FreeAudioTechnology/fat-violet/capsule/FAT array A/FAT_MEMS_Array_A1_2016-Feb-26_02-34-16AM-000_HOME.png

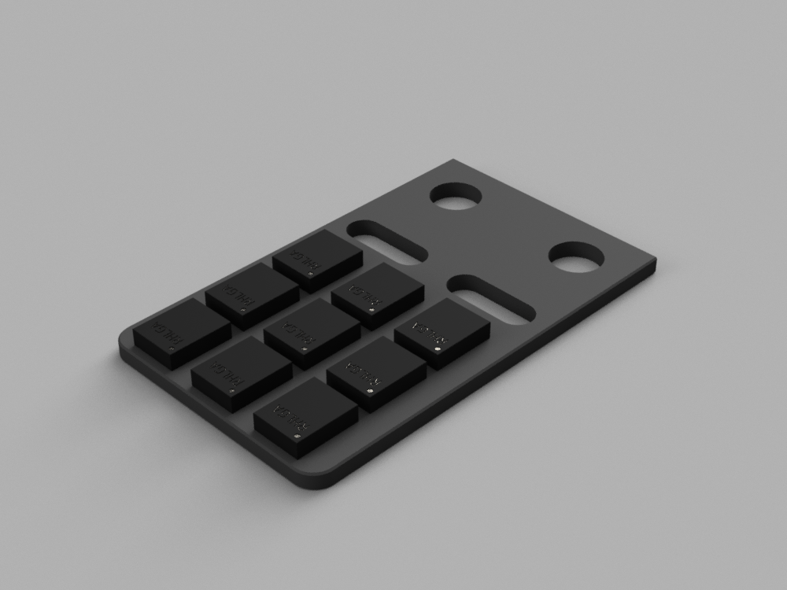
capsule/FAT array A/FAT_MEMS_Array_A1_2016-Feb-26_02-34-16AM-000_HOME.png
