FreeAudioTechnology/fat-violet/capsule/FAT capsule R/FAT Capsule R v2 cut1.png

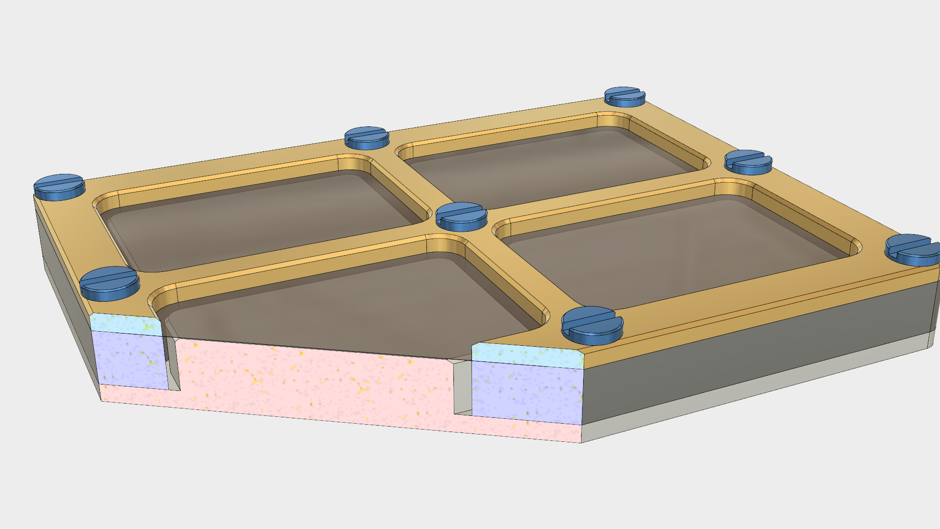
capsule/FAT capsule R/FAT Capsule R v2 cut1.png
