FreeAudioTechnology/fat-violet/capsule/FAT capsule R/FAT Capsule R v2 cut2.png

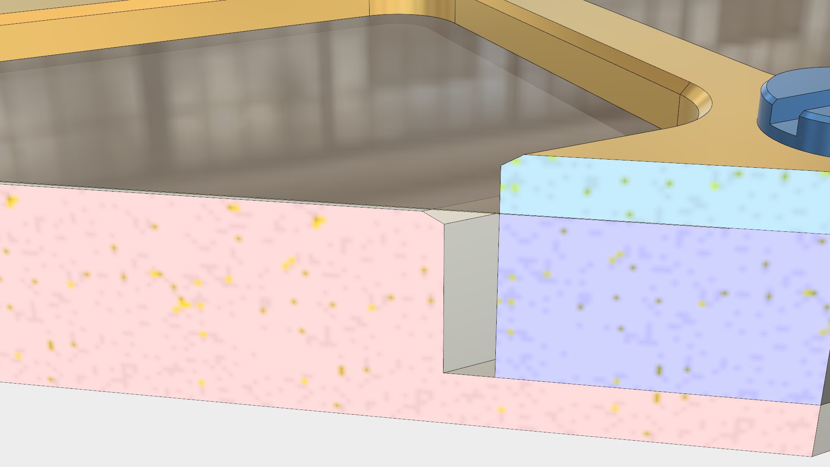
capsule/FAT capsule R/FAT Capsule R v2 cut2.png
