FreeAudioTechnology/fat-violet/capsule/FAT capsule R/FAT Capsule R v3.png

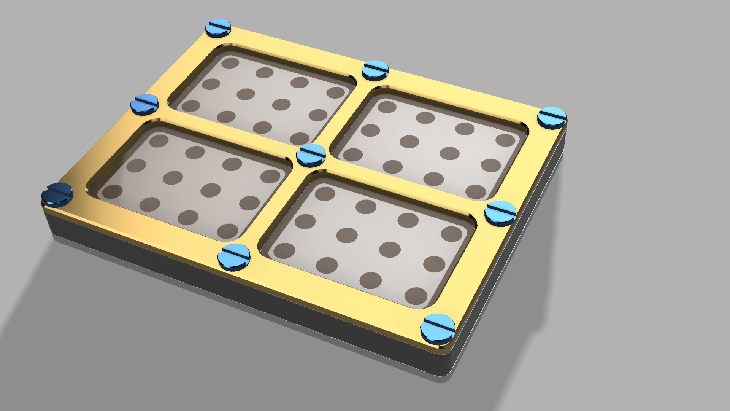
capsule/FAT capsule R/FAT Capsule R v3.png
