FreeAudioTechnology/fat-violet/case/misc/Fanatone Violet Microphone Case 1 v4.png

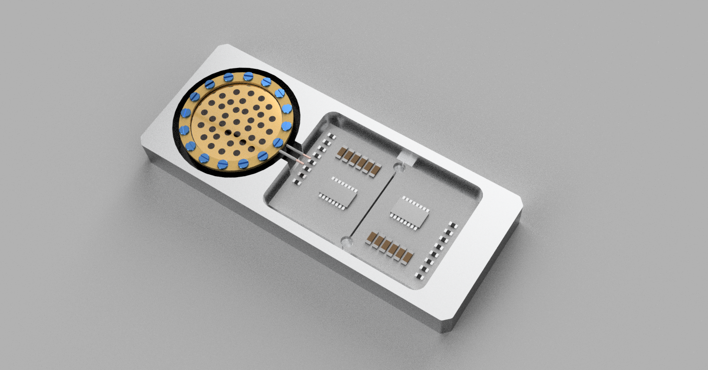
case/misc/Fanatone Violet Microphone Case 1 v4.png
