FreeAudioTechnology/fat-violet/case/misc/Fanatone Violet Microphone Case 1 v5.png

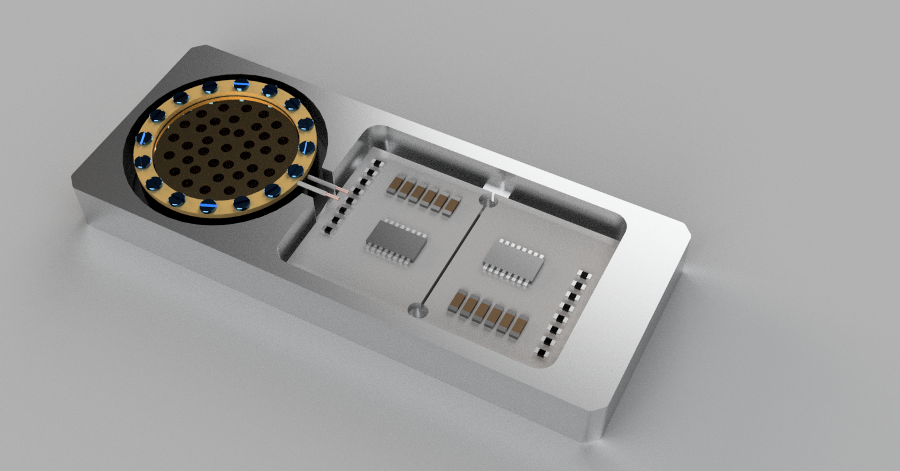
case/misc/Fanatone Violet Microphone Case 1 v5.png
