FreeAudioTechnology/fat-violet/case/misc/Fanatone Violet Microphone Case 1 v7 fibonacci sketch.png

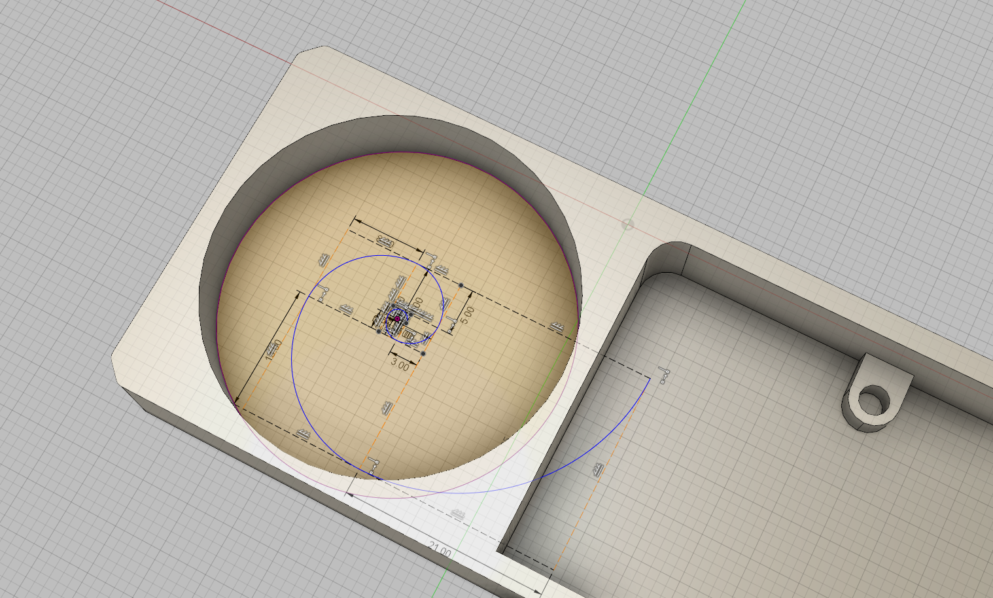
case/misc/Fanatone Violet Microphone Case 1 v7 fibonacci sketch.png
