FreeAudioTechnology/fat-violet/case/misc/Fanatone Violet Microphone Case 1 v7 fibonacci sunflower sketch.png

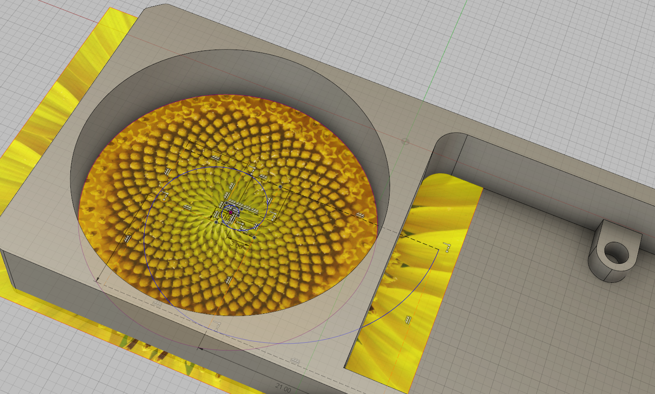
case/misc/Fanatone Violet Microphone Case 1 v7 fibonacci sunflower sketch.png
