FreeAudioTechnology/fat-violet/case/misc/Fanatone Violet Microphone Case 1 v8 hole pattern 1.png

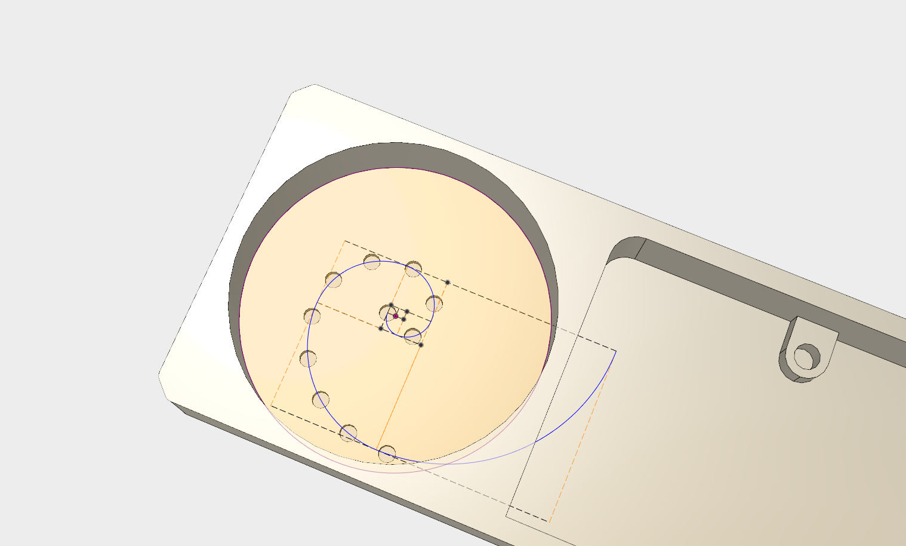
case/misc/Fanatone Violet Microphone Case 1 v8 hole pattern 1.png
