FreeAudioTechnology/fat-violet/case/misc/Fanatone Violet Microphone Case 1 v10 closed.png

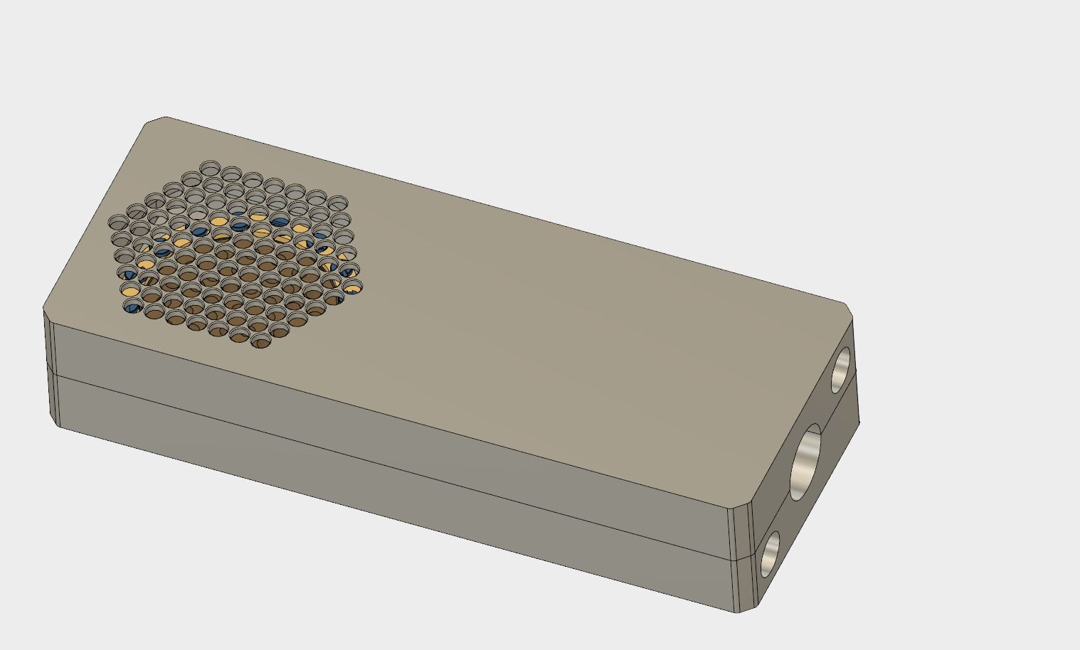
case/misc/Fanatone Violet Microphone Case 1 v10 closed.png
