FreeAudioTechnology/fat-violet/case/misc/Fanatone Violet Microphone Case 2 v2 slotted.png

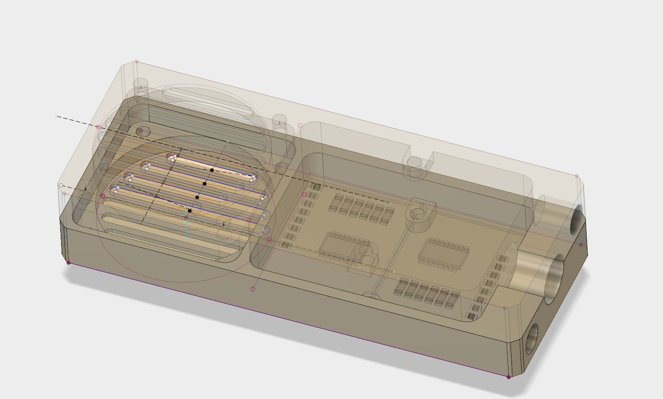
case/misc/Fanatone Violet Microphone Case 2 v2 slotted.png
