FreeAudioTechnology/fat-violet/case/misc/Fanatone Violet Microphone Case 2 v4 raytraced.png

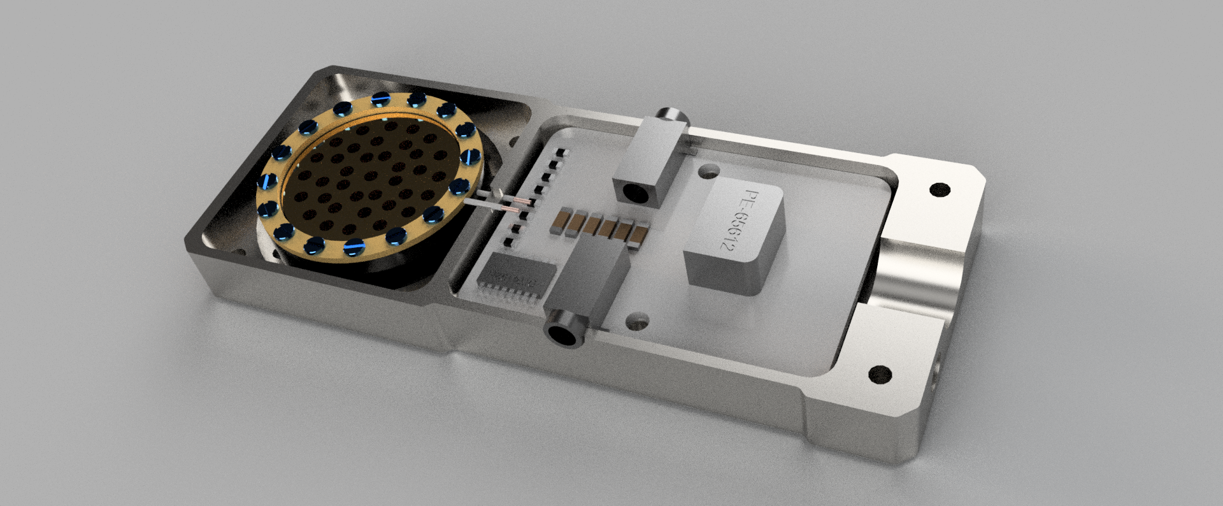
case/misc/Fanatone Violet Microphone Case 2 v4 raytraced.png
