FreeAudioTechnology/fat-violet/case/misc/Fanatone Violet Microphone Case 2 v4 rt bot tagged.png

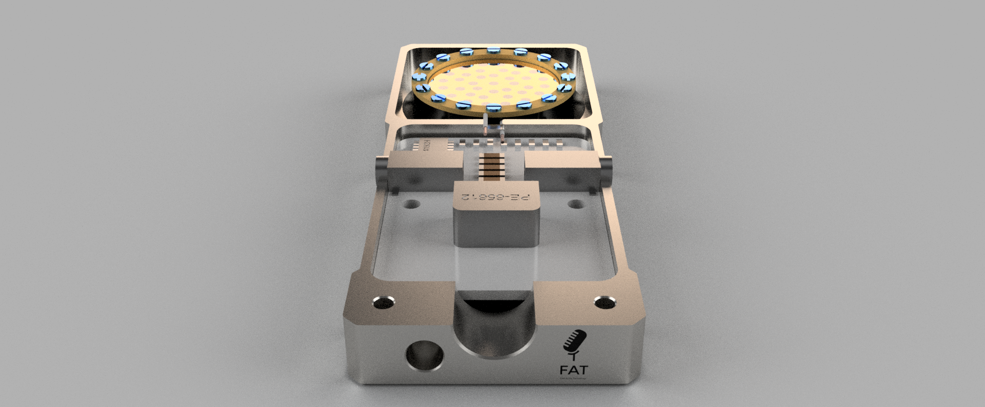
case/misc/Fanatone Violet Microphone Case 2 v4 rt bot tagged.png
