FreeAudioTechnology/fat-violet/case/misc/Fanatone Violet Microphone Case 2 v4 top.png

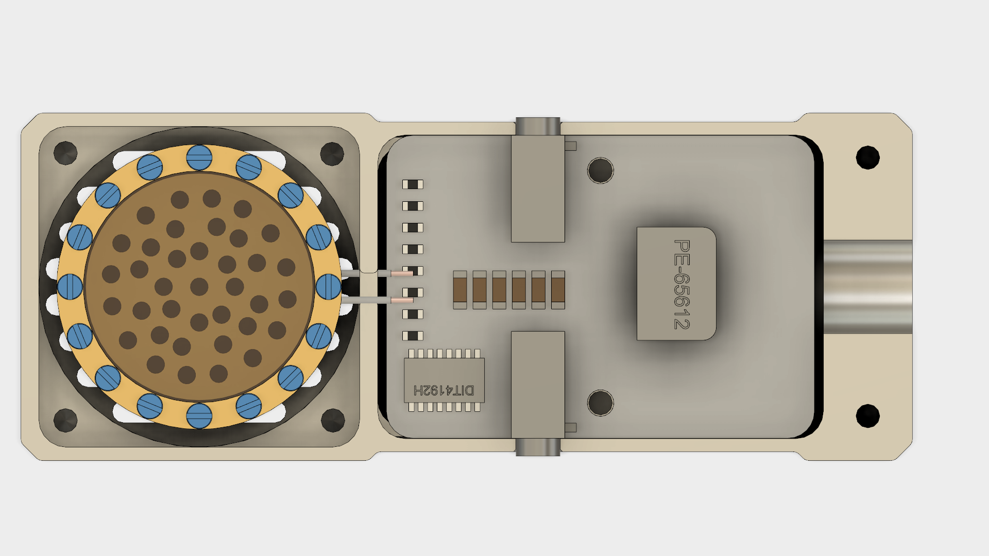
case/misc/Fanatone Violet Microphone Case 2 v4 top.png
