FreeAudioTechnology/fat-violet/pcb/ADC.png

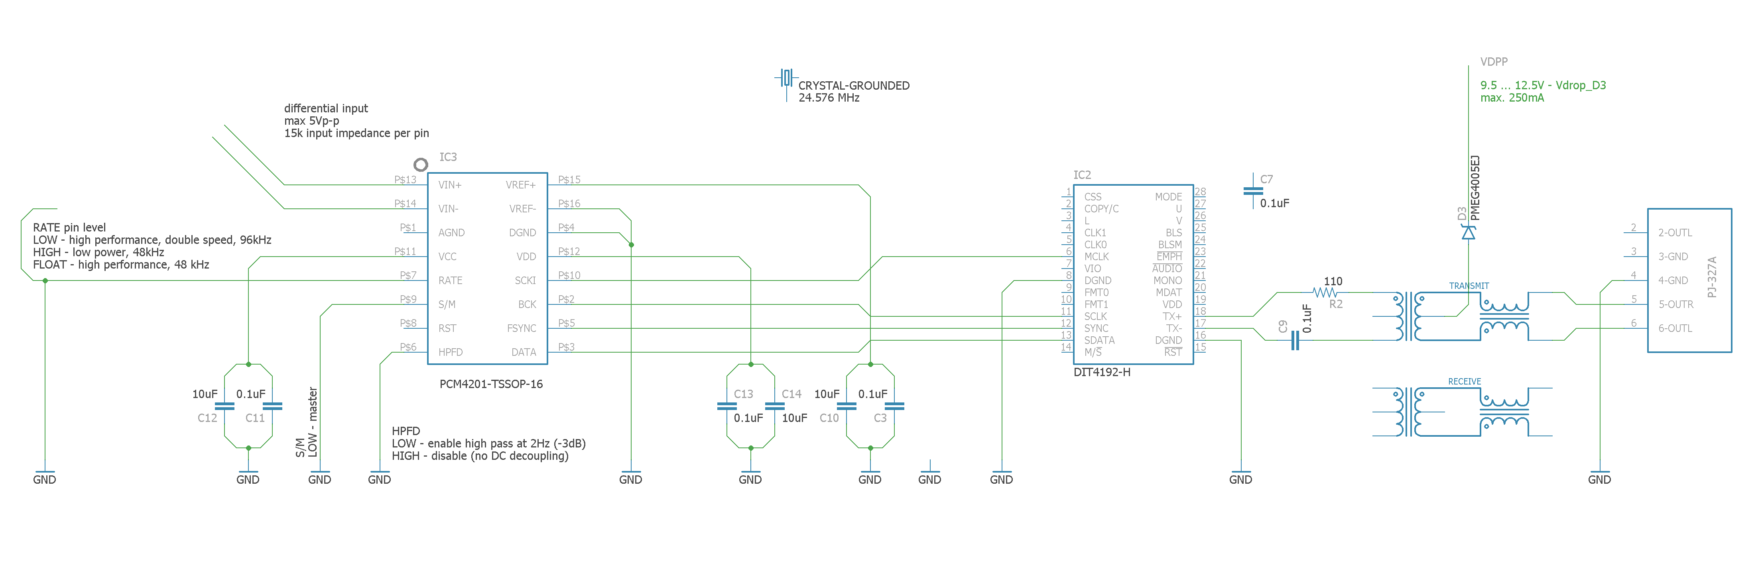
pcb/ADC.png
