FreeAudioTechnology/fat-violet/pcb/ChargePumpPCB-size-estimate.png

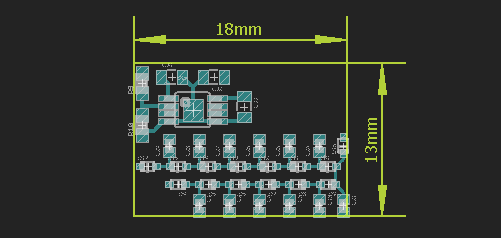
pcb/ChargePumpPCB-size-estimate.png
