FreeAudioTechnology/fat-violet/pcb/fanatone-adc-wip1-alpha.png

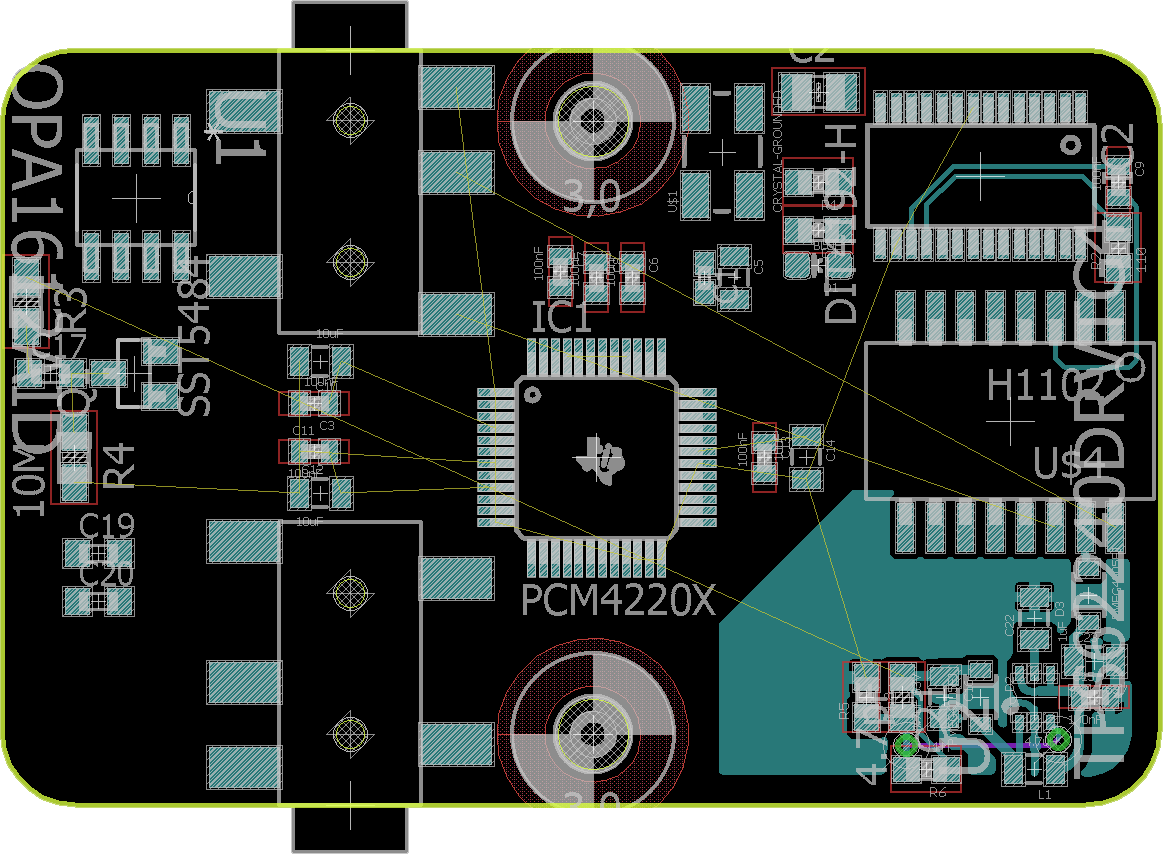
pcb/fanatone-adc-wip1-alpha.png
